adamioz-dev/HeaterControl/controler-main-nodemcu/include/OTAHandler.h

#ifndef OTA_CENTRALA_H
#define OTA_CENTRALA_H

// -------- includes --------

// -------- Global variables --------

// -------- Function definitions --------
void setup_ota();

void loop_ota();

#endif  //OTA_CENTRALA_H
